sparkfun/SparkFun_LG290P_Quadband_GNSS_RTK_Breakout/docs/assets/3d_model/poster.png

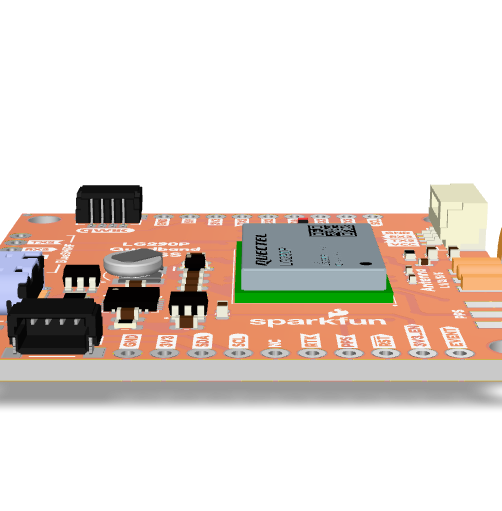
docs/assets/3d_model/poster.png
