sparkfun/SparkFun_LG290P_Quadband_GNSS_RTK_Breakout/docs/assets/img/hookup_guide/assembly-openlog_top.jpg

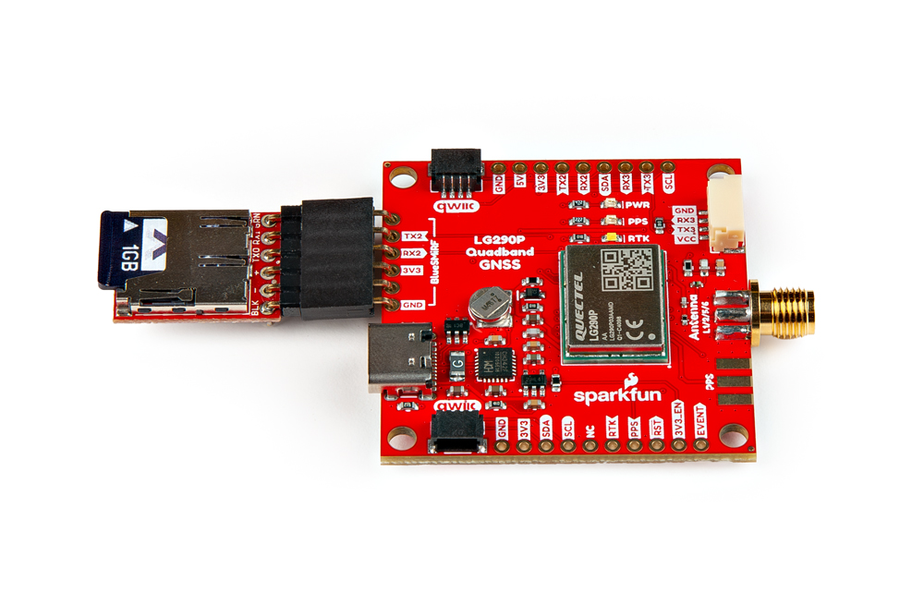
docs/assets/img/hookup_guide/assembly-openlog_top.jpg
