sparkfun/SparkFun_LG290P_Quadband_GNSS_RTK_Breakout/docs/assets/img/hookup_guide/LG290P-top_original.png

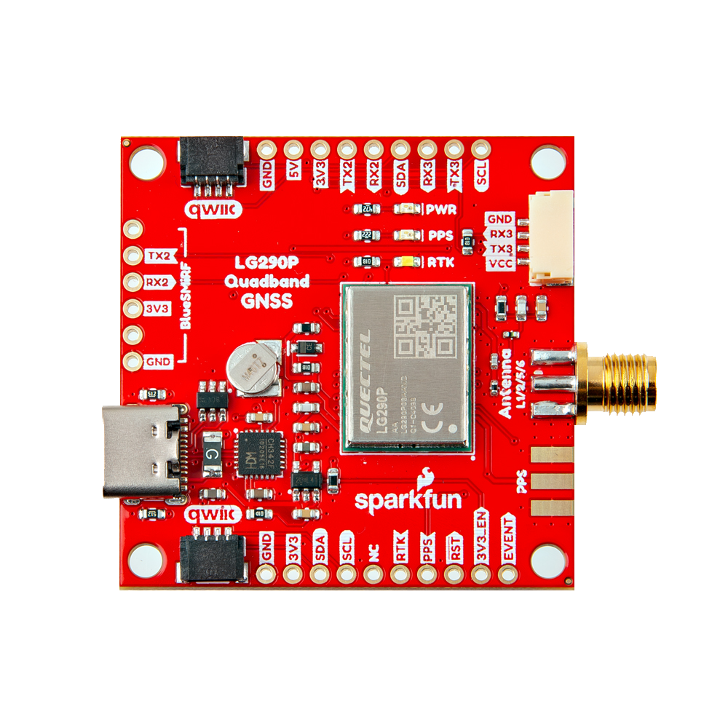
docs/assets/img/hookup_guide/LG290P-top_original.png
