sparkfun/SparkFun_LG290P_Quadband_GNSS_RTK_Breakout/docs/assets/img/hookup_guide/pin-uart.png

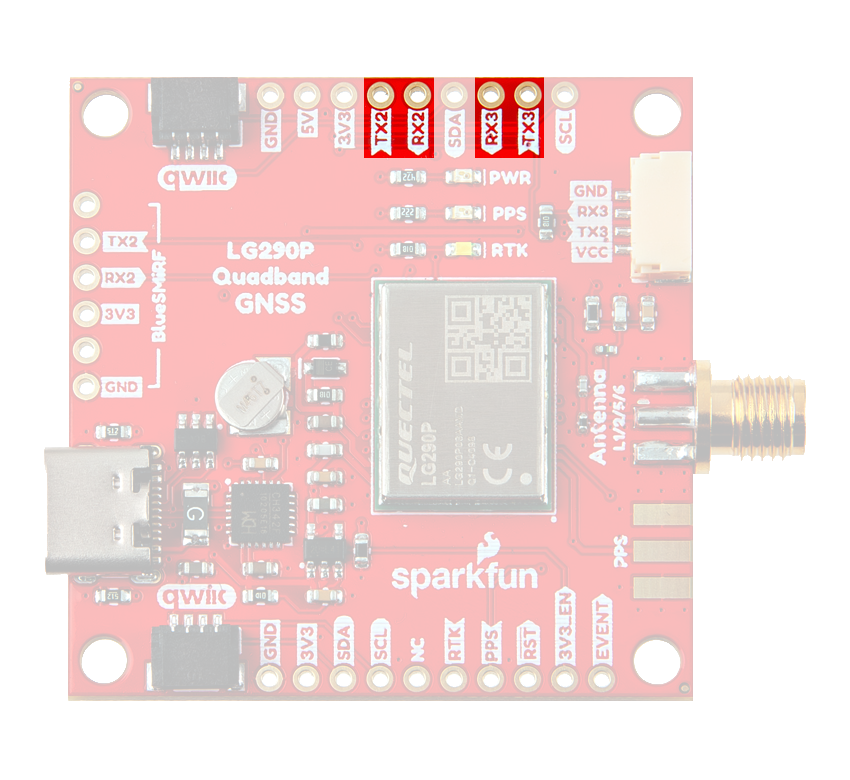
docs/assets/img/hookup_guide/pin-uart.png
