sparkfun/SparkFun_LG290P_Quadband_GNSS_RTK_Breakout/docs/assets/img/hookup_guide/uart2.png

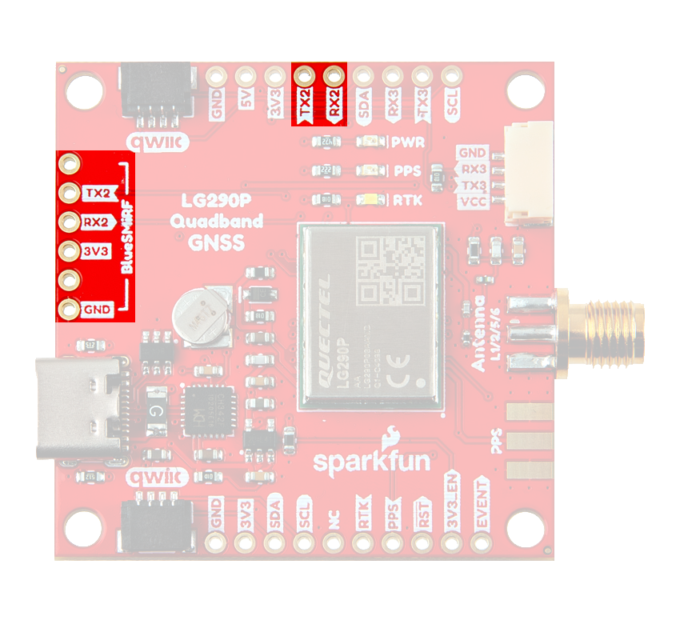
docs/assets/img/hookup_guide/uart2.png
